Angoosh/Stargate_LSD/Software/SoundData.h

/*
byte kokoton_warning[] = {
0x52, 0x49, 0x46, 0x46, 0x86, 0xBD, 0x00, 0x00, 0x57, 0x41, 0x56, 0x45, 0x66, 0x6D, 0x74, 0x20, 
0x10, 0x00, 0x00, 0x00, 0x01, 0x00, 0x01, 0x00, 0x40, 0x1F, 0x00, 0x00, 0x80, 0x3E, 0x00, 0x00, 
0x02, 0x00, 0x10, 0x00, 0x64, 0x61, 0x74, 0x61, 0x62, 0xBD, 0x00, 0x00, 0x00, 0x00, 0x00, 0x00, 
0x00, 0x00, 0xFF, 0xFF, 0x03, 0x00, 0xFC, 0xFF, 0x03, 0x00, 0xFF, 0xFF, 0xFE, 0xFF, 0x05, 0x00, 
0xFA, 0xFF, 0x06, 0x00, 0xFA, 0xFF, 0x05, 0x00, 0xFC, 0xFF, 0x04, 0x00, 0xFD, 0xFF, 0x00, 0x00, 
0x01, 0x00, 0x00, 0x00, 0xFF, 0xFF, 0x01, 0x00, 0xFE, 0xFF, 0x03, 0x00, 0xFD, 0xFF, 0x02, 0x00, 
0xF9, 0xFF, 0xF6, 0xFF, 0xF8, 0xFF, 0xF9, 0xFF, 0xFB, 0xFF, 0x06, 0x00, 0x02, 0x00, 0x02, 0x00, 
0x01, 0x00, 0x06, 0x00, 0x05, 0x00, 0x0A, 0x00, 0x06, 0x00, 0x03, 0x00, 0x03, 0x00, 0x04, 0x00, 
0xF7, 0xFF, 0xFF, 0xFF, 0xF3, 0xFF, 0x01, 0x00, 0xFE, 0xFF, 0x06, 0x00, 0x03, 0x00, 0x06, 0x00, 
0x07, 0x00, 0x10, 0x00, 0x07, 0x00, 0x0E, 0x00, 0x01, 0x00, 0x06, 0x00, 0x00, 0x00, 0x03, 0x00, 
0x01, 0x00, 0x01, 0x00, 0xFA, 0xFF, 0xFC, 0xFF, 0xFA, 0xFF, 0x04, 0x00, 0xFA, 0xFF, 0x03, 0x00, 
0xFD, 0xFF, 0xFE, 0xFF, 0xF9, 0xFF, 0xF7, 0xFF, 0xFB, 0xFF, 0xFA, 0xFF, 0xF6, 0xFF, 0xF8, 0xFF, 
0xF7, 0xFF, 0xF7, 0xFF, 0xFB, 0xFF, 0xF9, 0xFF, 0xFF, 0xFF, 0xF8, 0xFF, 0xFB, 0xFF, 0xF6, 0xFF, 
0xFD, 0xFF, 0xFA, 0xFF, 0xFE, 0xFF, 0xFE, 0xFF, 0x05, 0x00, 0xFB, 0xFF, 0x05, 0x00, 0x06, 0x00, 
0x04, 0x00, 0x0E, 0x00, 0xFF, 0xFF, 0x0D, 0x00, 0xFD, 0xFF, 0x07, 0x00, 0xFF, 0xFF, 0x04, 0x00, 
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
  0x86, 0x84, 0x7d, 0x79, 0x76, 0x77, 0x79, 0x7c, 0x78, 0x81, 0x80, 0x7d, 0x82, 0x7c, 0x81, 0x7d, 
  0x79, 0x7d, 0x7e, 0x7a, 0x79, 0x7b, 0x75, 0x7b, 0x84, 0x89, 0x8b, 0x8d, 0x98, 0x95, 0x9f, 0xa1, 
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
};
